SurvivalHacking/HandRFID/HandRFID12C/FreeSansBold12pt8b.h

// FreeSansBold12pt8b - FreeSans Latin-1 (0x20-0xFF) for Adafruit GFX / TFT_eSPI
// Generated with fontconvert from GNU FreeFont TTF
// Covers full French, Italian, German, Spanish accented characters
#pragma once
#include <Adafruit_GFX.h>

const uint8_t FreeSansBold12pt8bBitmaps[] PROGMEM = {
  0x00, 0xFF, 0xFF, 0xFF, 0xFF, 0x76, 0x66, 0x60, 0xFF, 0xF0, 0xF3, 0xFC,
  0xFF, 0x3F, 0xCF, 0x61, 0x98, 0x60, 0x0E, 0x70, 0x73, 0x83, 0x18, 0xFF,
  0xF7, 0xFF, 0xBF, 0xFC, 0x73, 0x83, 0x18, 0x18, 0xC7, 0xFF, 0xBF, 0xFD,
  0xFF, 0xE3, 0x18, 0x39, 0xC1, 0xCE, 0x0E, 0x70, 0x02, 0x00, 0x70, 0x0F,
  0xF8, 0x7F, 0xE7, 0xAF, 0xB9, 0x3D, 0xC8, 0x0F, 0x40, 0x3F, 0x00, 0xFF,
  0x00, 0xFC, 0x05, 0xFF, 0x27, 0xF9, 0x3F, 0xEB, 0xEF, 0xFE, 0x3F, 0xE0,
  0xFC, 0x00, 0x80, 0x04, 0x00, 0x3C, 0x06, 0x0F, 0xC1, 0x81, 0xFC, 0x30,
  0x73, 0x8C, 0x0C, 0x31, 0x81, 0xCE, 0x60, 0x1F, 0xCC, 0x03, 0xF3, 0x00,
  0x3C, 0x67, 0x80, 0x19, 0xF8, 0x02, 0x7F, 0x80, 0xCE, 0x70, 0x11, 0x86,
  0x06, 0x39, 0xC1, 0x87, 0xF8, 0x30, 0x7E, 0x0C, 0x07, 0x80, 0x07, 0x80,
  0x1F, 0xC0, 0x3F, 0xE0, 0x3C, 0xE0, 0x3C, 0xE0, 0x3E, 0xE0, 0x0F, 0xC0,
  0x07, 0x00, 0x3F, 0x8C, 0x7F, 0xCC, 0xF1, 0xFC, 0xF0, 0xF8, 0xF0, 0x78,
  0xF8, 0xF8, 0x7F, 0xFC, 0x3F, 0xDE, 0x1F, 0x8E, 0xFF, 0xFF, 0x66, 0x0C,
  0x73, 0x8E, 0x71, 0xC7, 0x38, 0xE3, 0x8E, 0x38, 0xE3, 0x8E, 0x1C, 0x71,
  0xC3, 0x8E, 0x18, 0x70, 0xC3, 0x87, 0x1C, 0x38, 0xE3, 0x87, 0x1C, 0x71,
  0xC7, 0x1C, 0x71, 0xCE, 0x38, 0xE7, 0x1C, 0x63, 0x80, 0x10, 0x23, 0x5F,
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
  {   794,  12,  18,  15,    2,  -17 },   // 0x46 'F'
  {   821,  16,  18,  19,    1,  -17 },   // 0x47 'G'
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

const GFXfont FreeSansBold12pt8b PROGMEM = {
  (uint8_t  *)FreeSansBold12pt8bBitmaps,
  (GFXglyph *)FreeSansBold12pt8bGlyphs,
  0x20, 0xFF, 26 };

// Approx. 8027 bytes
